boert/KC85__PK2_Pruefmodul/Bilder/Modul_PK2_oben.jpg

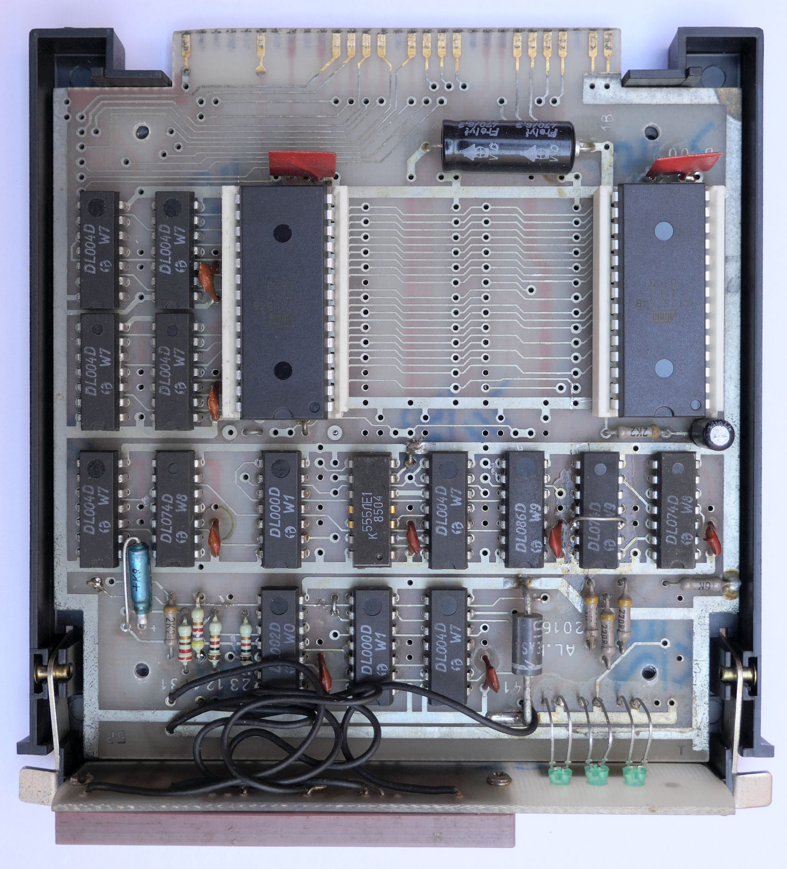
Bilder/Modul_PK2_oben.jpg
